dirkbeer/Helium-Bridge/_pictures/breadboard_prototype/IMG_20230515_084315_530.jpg

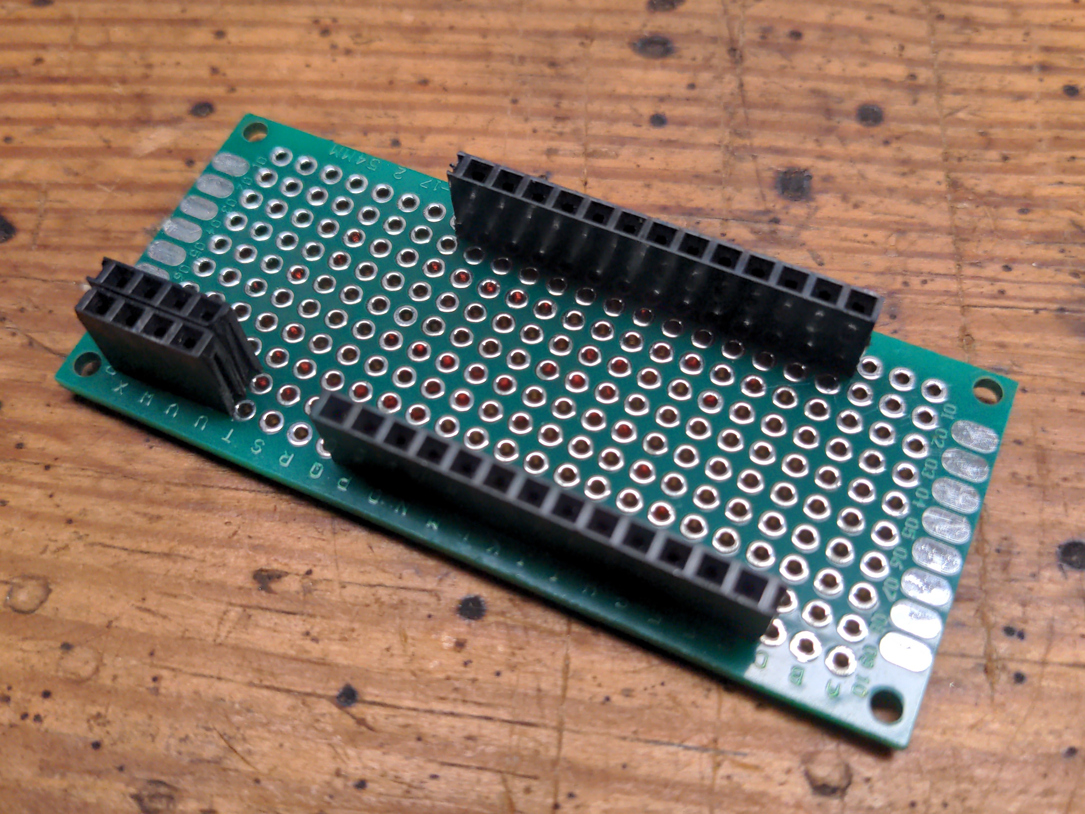
_pictures/breadboard_prototype/IMG_20230515_084315_530.jpg
