dirkbeer/Helium-Bridge/_pictures/PXL_20230918_185547411.jpg

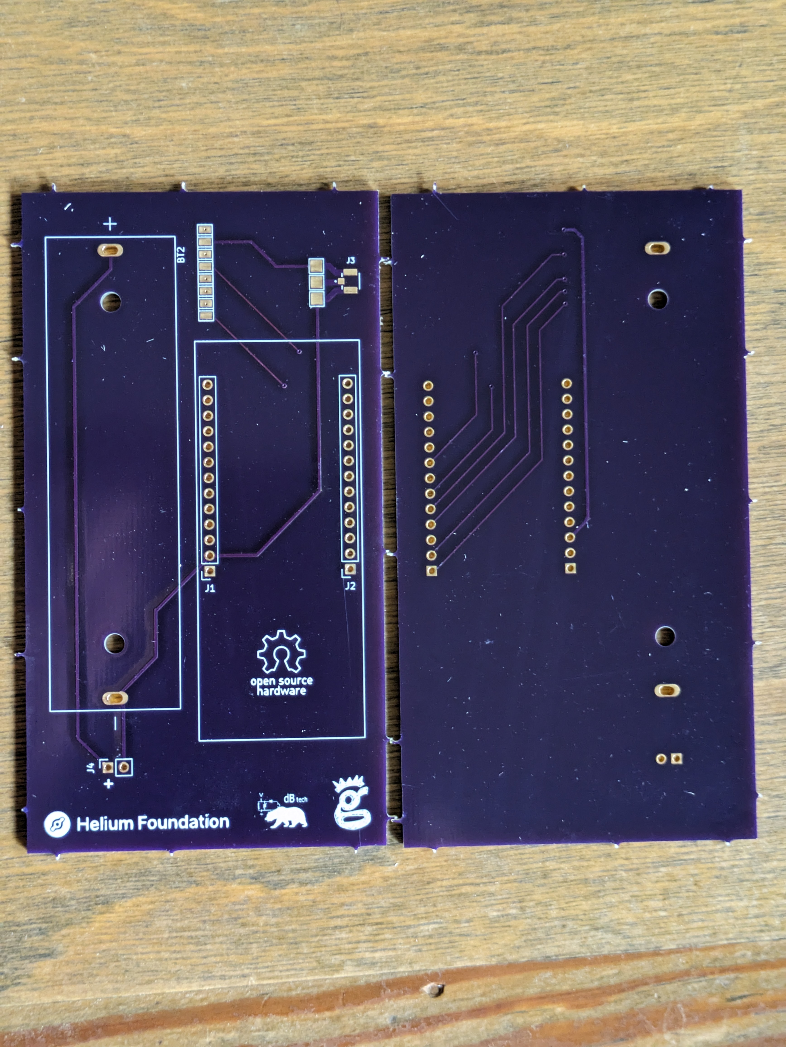
_pictures/PXL_20230918_185547411.jpg
